GarrettBardini/EnvironmentSensor/PythonScripts/ImageCapture.py

#!/usr/bin/env python3
#################################################################
#####     IMAGE CAPTURE | CAPTURE DATA FOR TIMELAPSE        #####
#####     AUTHOR: GARRETT PETER BARDINI (GPB)               #####
#####     CREATE_DATE: 2022/10/14                           #####
#####     LAST_MODIFIED: 2024/08/21                         #####
#################################################################
import os
import time
import cv2
import datetime
workingdir = (r"/mnt/usb0/TimelapseImages")

def capture_image():
    timestamp = datetime.datetime.now().strftime('%Y%m%d')
    filename = timestamp + 'ImageCapture.jpg'
    cam = cv2.VideoCapture(0)
    attempts = 0
    while attempts < 125:
        ret, image = cam.read()
        attempts += 1
        
    cv2.imwrite(os.path.join(workingdir,filename), image)
    cam.release()
    cv2.destroyAllWindows()

dt = datetime.datetime.now()
secondsToMidnight = (((24 - dt.hour - 1) * 60 * 60) + ((60 - dt.minute - 1) * 60) + (60 - dt.second))
time.sleep(secondsToMidnight)
while True:
    capture_image() # Do I Need Retrys?
    time.sleep(24*60*60)# Wait till tomorrow 
